ignasrum/headphones/docs/images/image_1.jpg

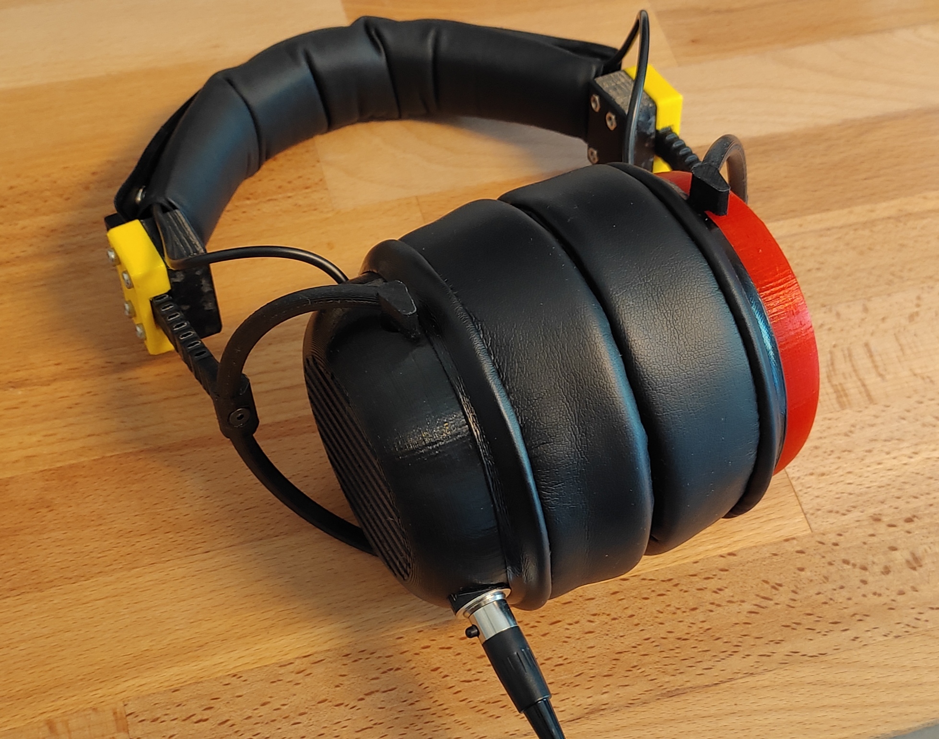
docs/images/image_1.jpg
