ignasrum/headphones/docs/images/image_3.jpg

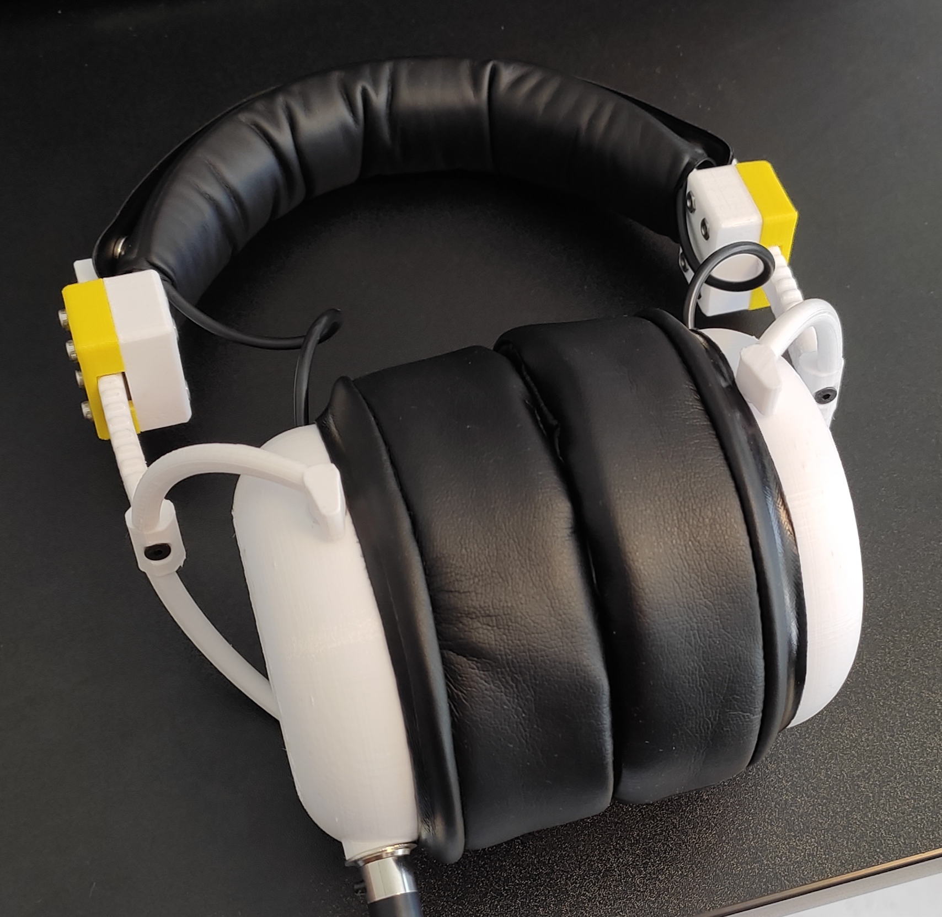
docs/images/image_3.jpg
